nickleassdimebutt/usbc-3v3/output/docs/hierarchical/schematic_block_header.png

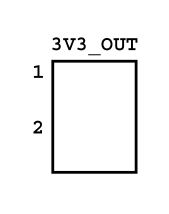
output/docs/hierarchical/schematic_block_header.png
