nickleassdimebutt/usbc-3v3/output/docs/hierarchical/schematic_block_ldo.png

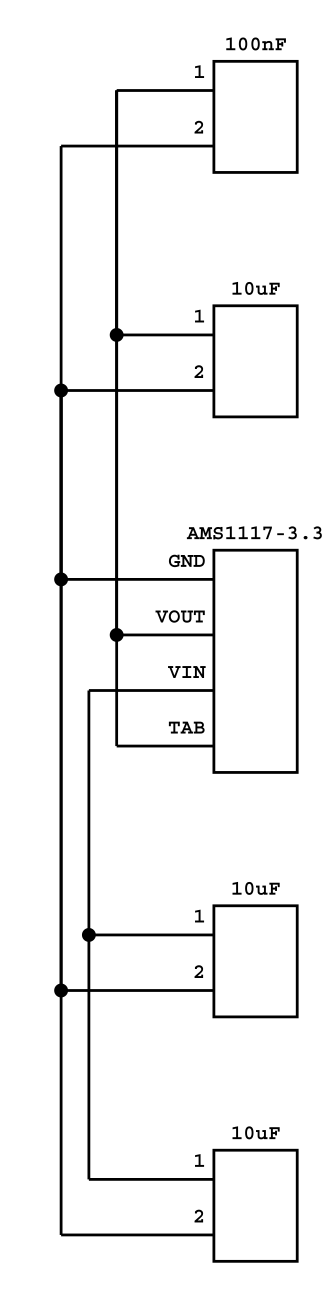
output/docs/hierarchical/schematic_block_ldo.png
