nickleassdimebutt/usbc-3v3/output/docs/hierarchical/schematic_overview.png

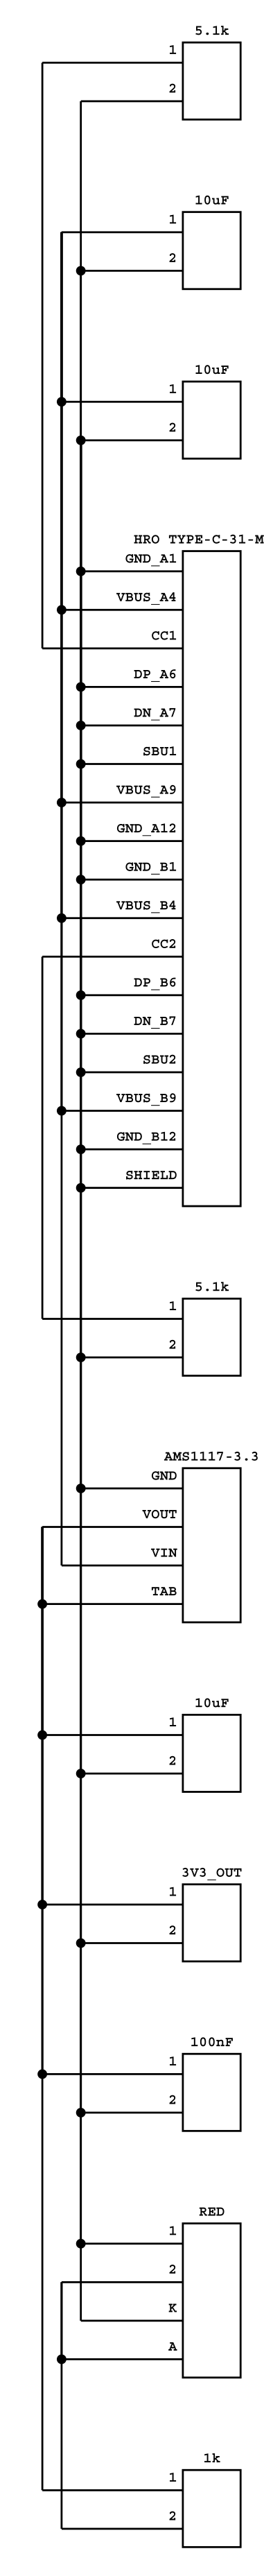
output/docs/hierarchical/schematic_overview.png
