nickleassdimebutt/usbc-3v3/output/render/pcbdraw_back.png

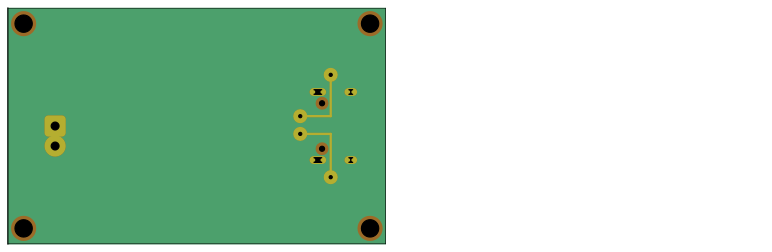
output/render/pcbdraw_back.png
