nickleassdimebutt/usbc-3v3/output/render/pcbdraw_front.png

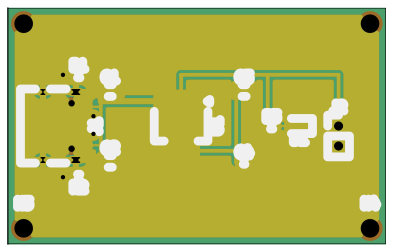
output/render/pcbdraw_front.png
