nickleassdimebutt/usbc-3v3/output/render/render_bottom.png

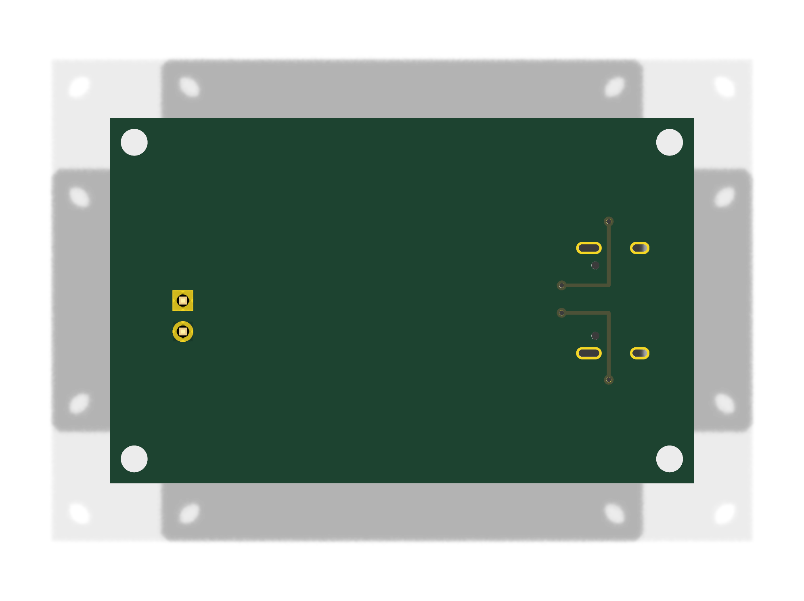
output/render/render_bottom.png
