nickleassdimebutt/usbc-3v3/output/render/render_top.png

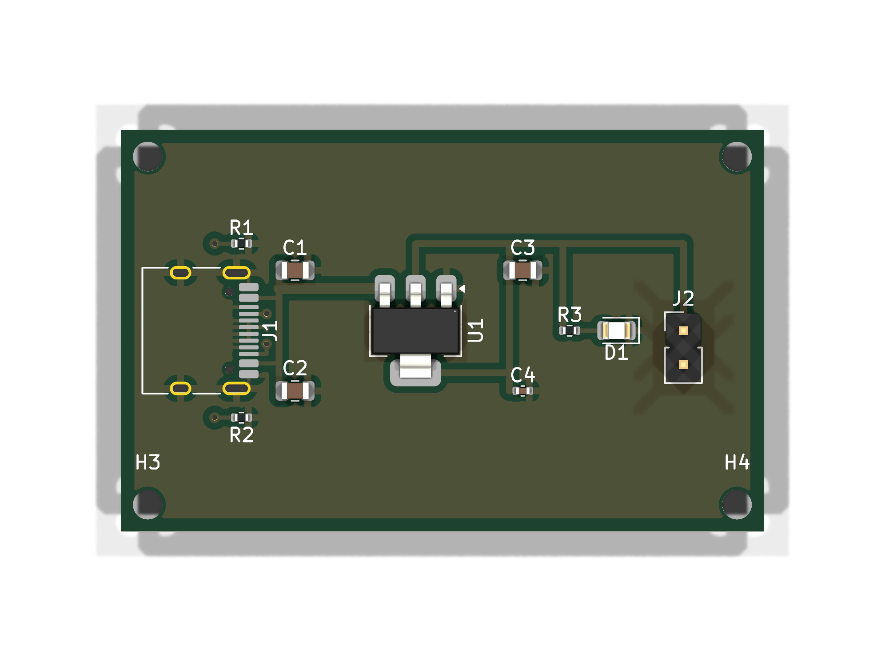
output/render/render_top.png
