nickleassdimebutt/usbc-3v3/output/sim/line_reg.png

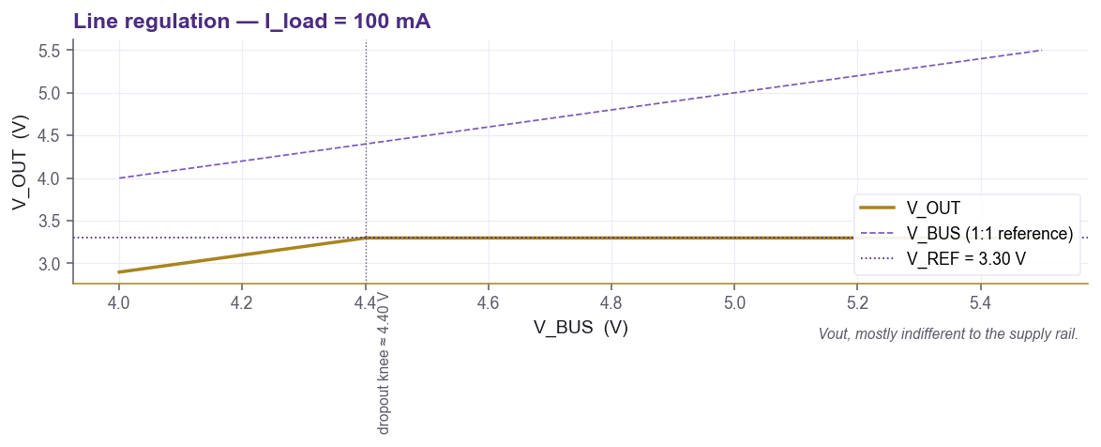
output/sim/line_reg.png
