nickleassdimebutt/usbc-3v3/output/sim/load_reg.png

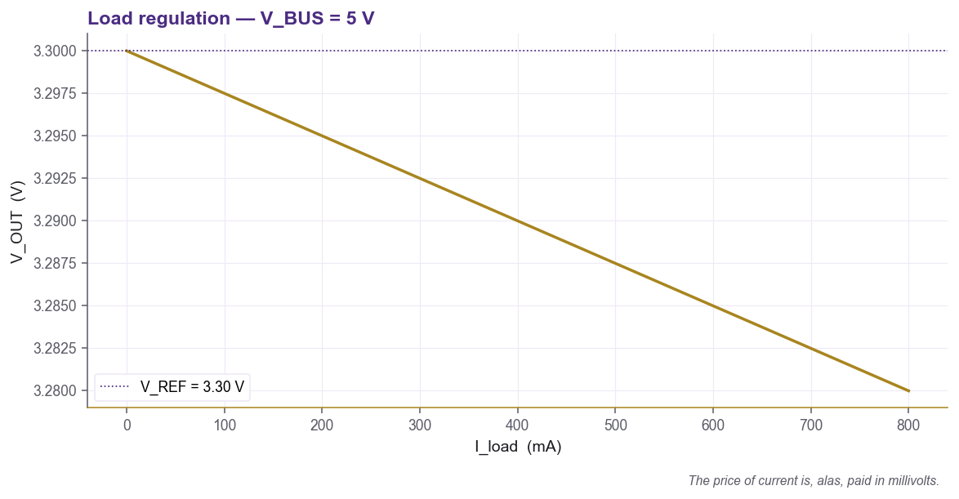
output/sim/load_reg.png
