nickleassdimebutt/usbc-3v3/output/sim/monte_carlo.png

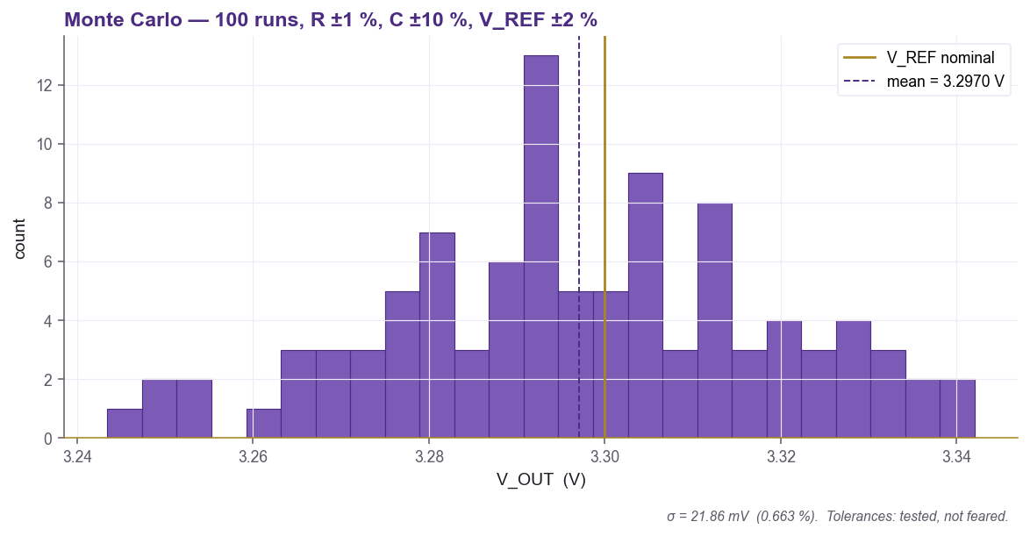
output/sim/monte_carlo.png
