nickleassdimebutt/usbc-3v3/output/sim/property_vout.png

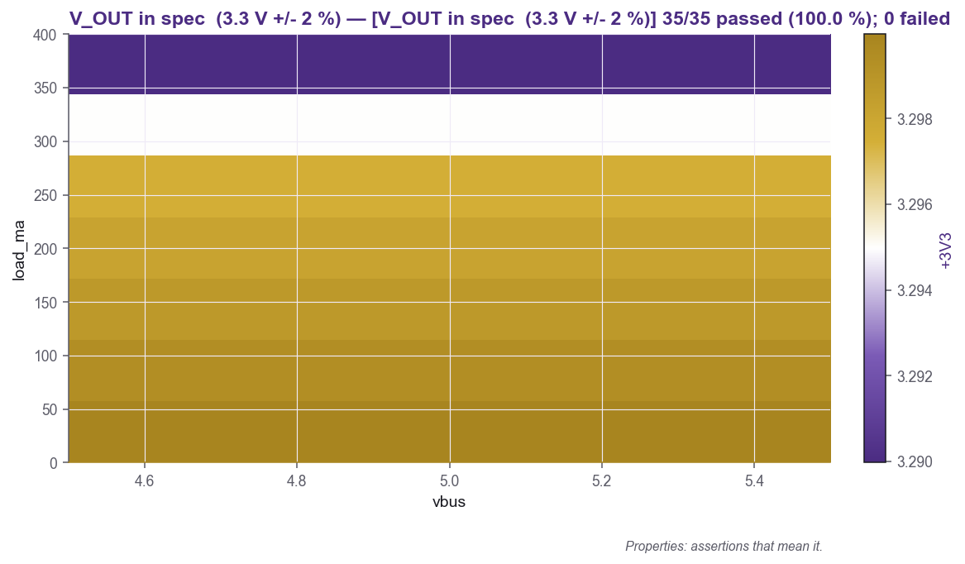
output/sim/property_vout.png
