nickleassdimebutt/usbc-3v3/output/sim/temp_sweep.png

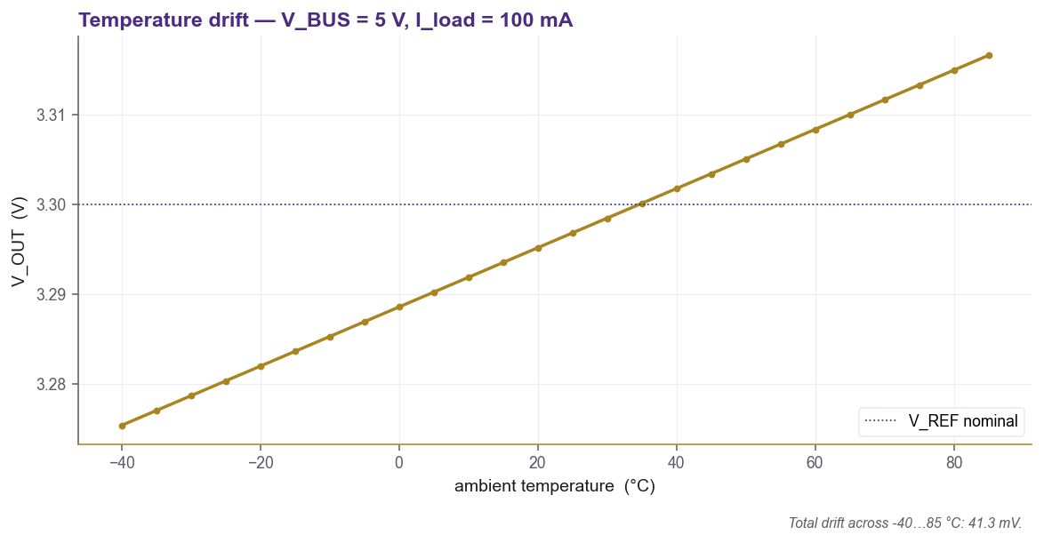
output/sim/temp_sweep.png
