nickleassdimebutt/usbc-3v3/output/sim/load_step.png

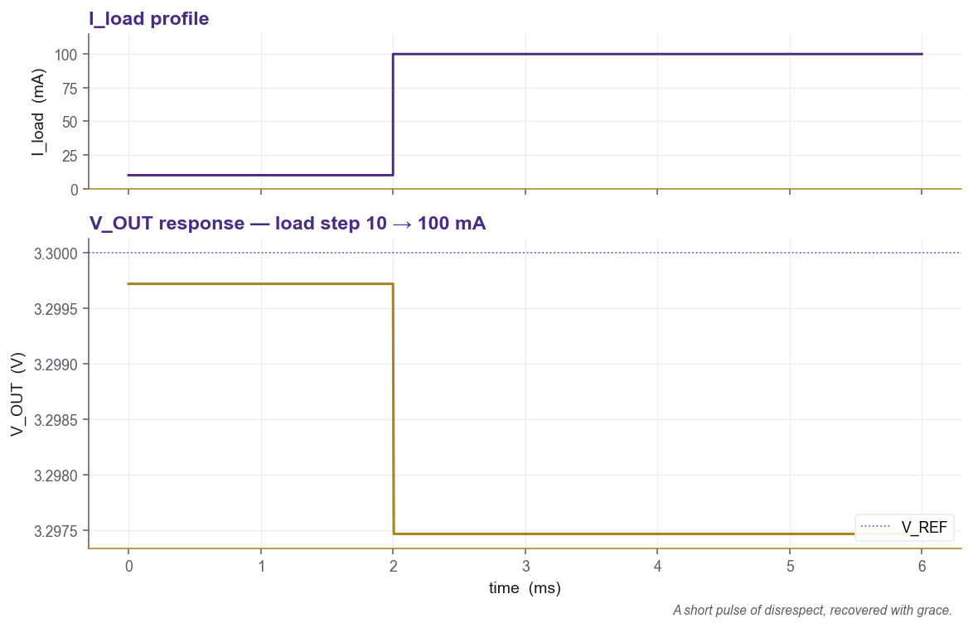
output/sim/load_step.png
